DanielFloresElias/MinairoV1.0/DOCs/CatSkills2023/Modul_1/PistaDemo.PNG

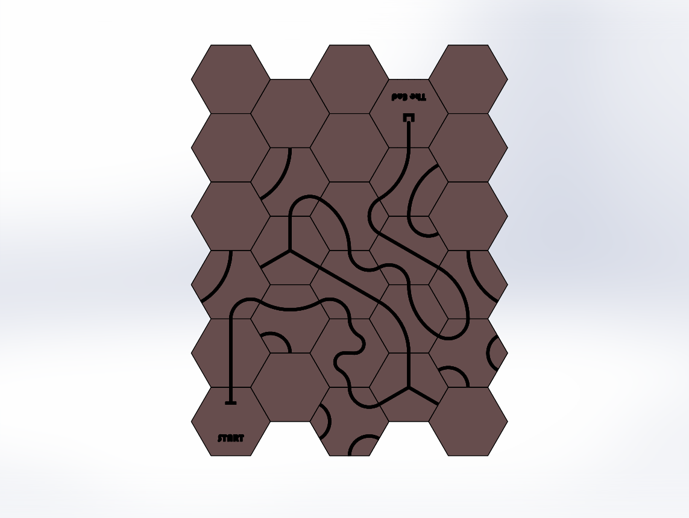
DOCs/CatSkills2023/Modul_1/PistaDemo.PNG
