DanielFloresElias/MinairoV1.0/Hardware/Firmware/Slave0_Sensors/Documents/Pololu Driverjpg.jpg

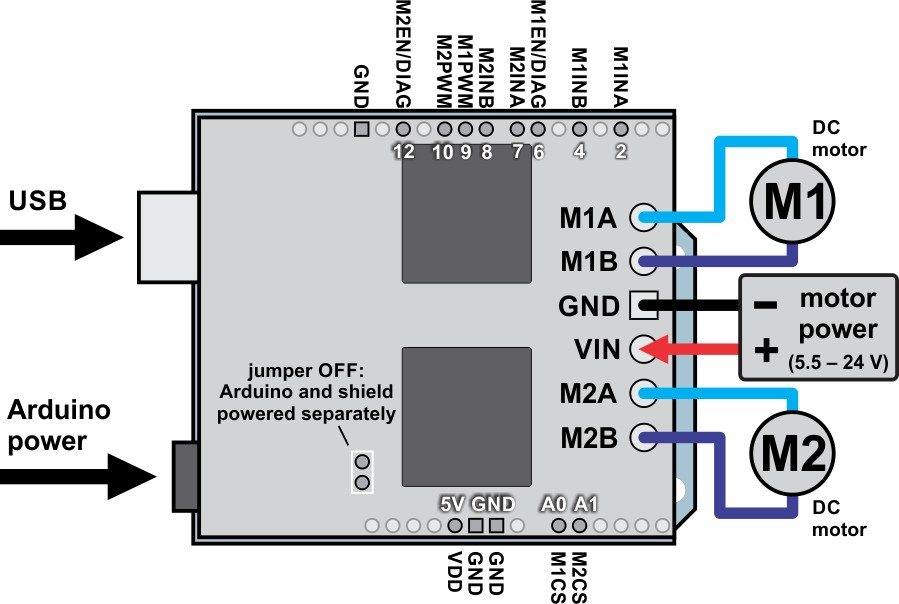
Hardware/Firmware/Slave0_Sensors/Documents/Pololu Driverjpg.jpg
