DanielFloresElias/MinairoV1.0/Hardware/Firmware/Slave0_Sensors/Documents/WhatsApp Image 2022-01-12 at 19.06.40.jpeg

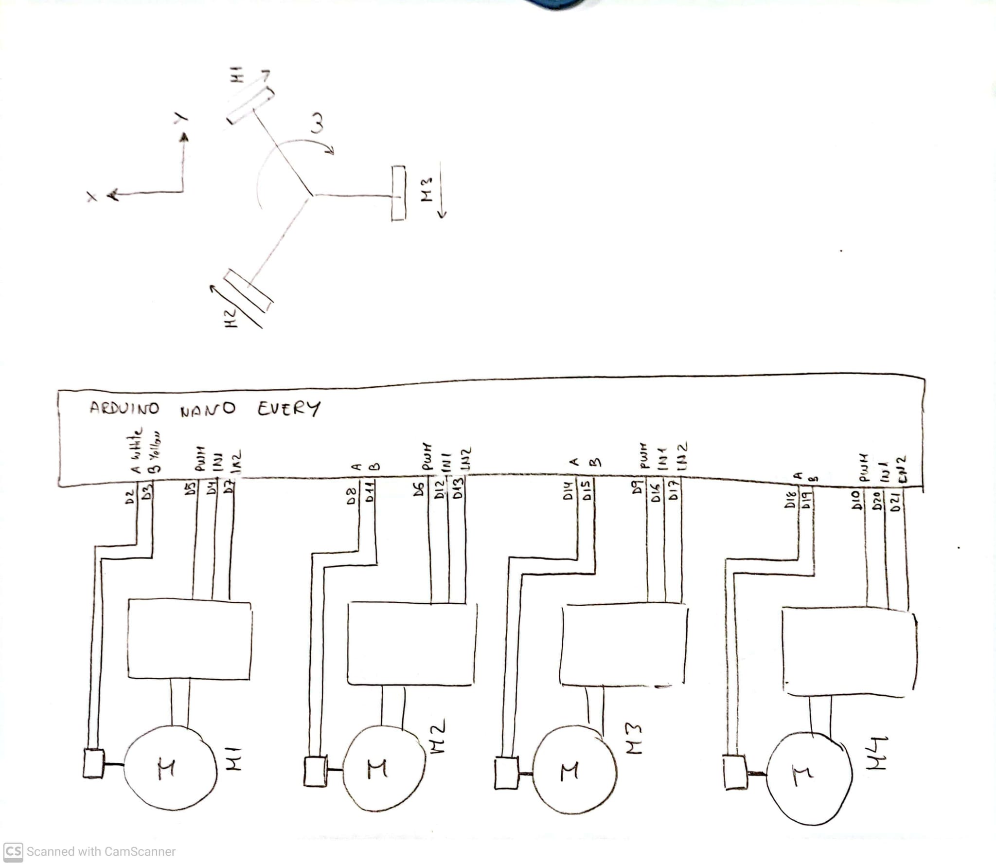
Hardware/Firmware/Slave0_Sensors/Documents/WhatsApp Image 2022-01-12 at 19.06.40.jpeg
