DanielFloresElias/MinairoV1.0/Hardware/STLs/Llapis/IMG/img_pen03.jpeg

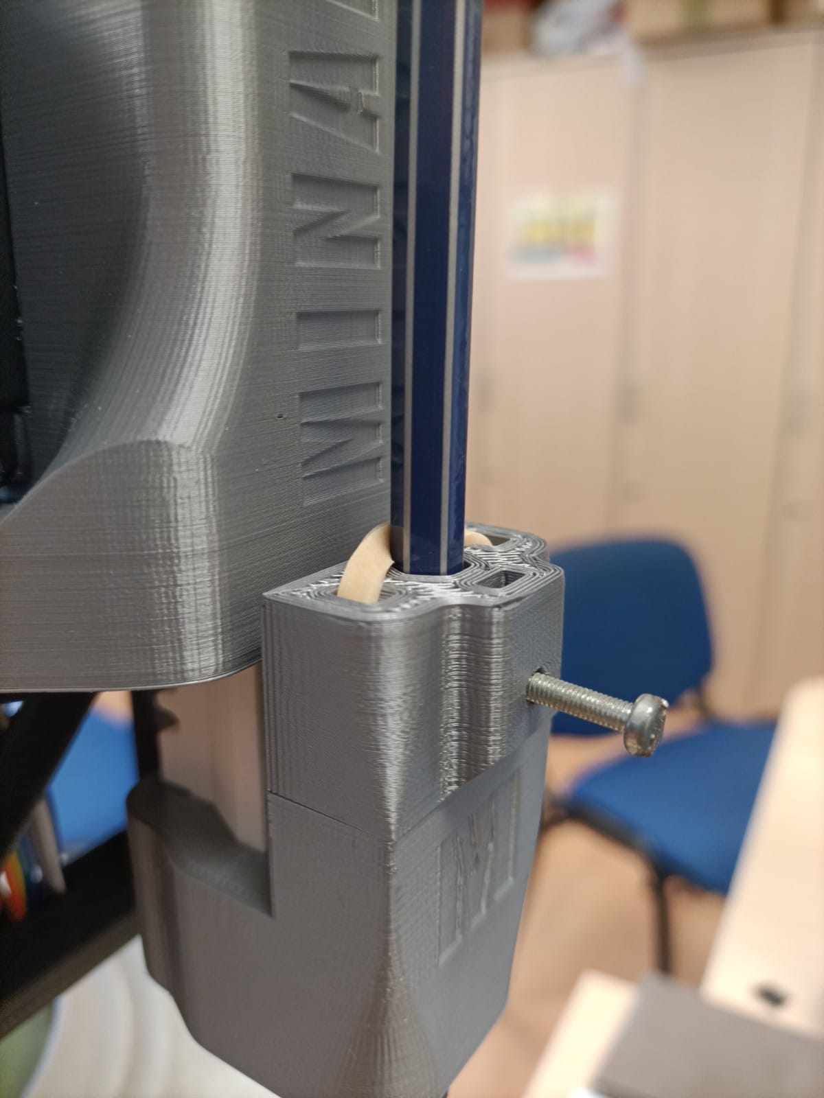
Hardware/STLs/Llapis/IMG/img_pen03.jpeg
