DanielFloresElias/MinairoV1.0/IMG/BackSide.png

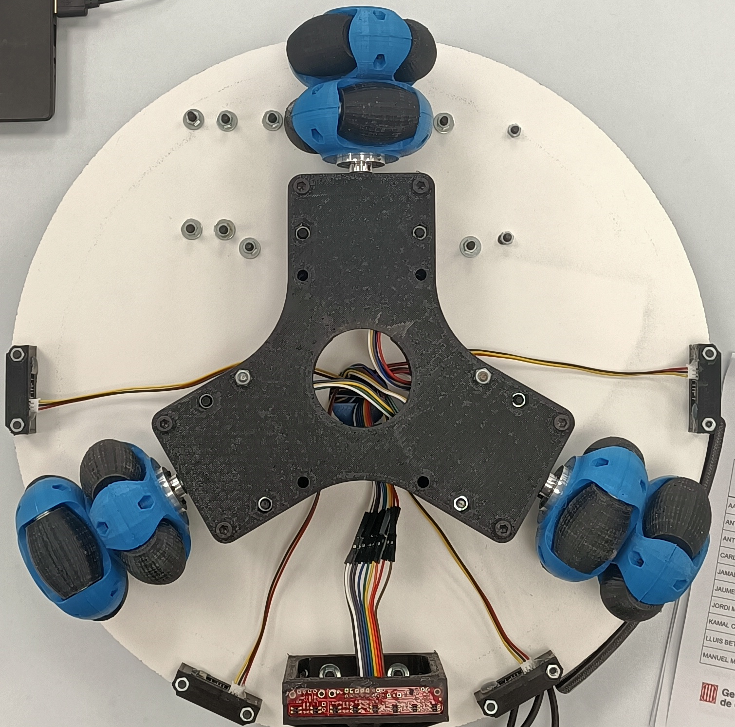
IMG/BackSide.png
