DanielFloresElias/MinairoV1.0/IMG/bateria-cecotec-conga-excellence-990.jpg

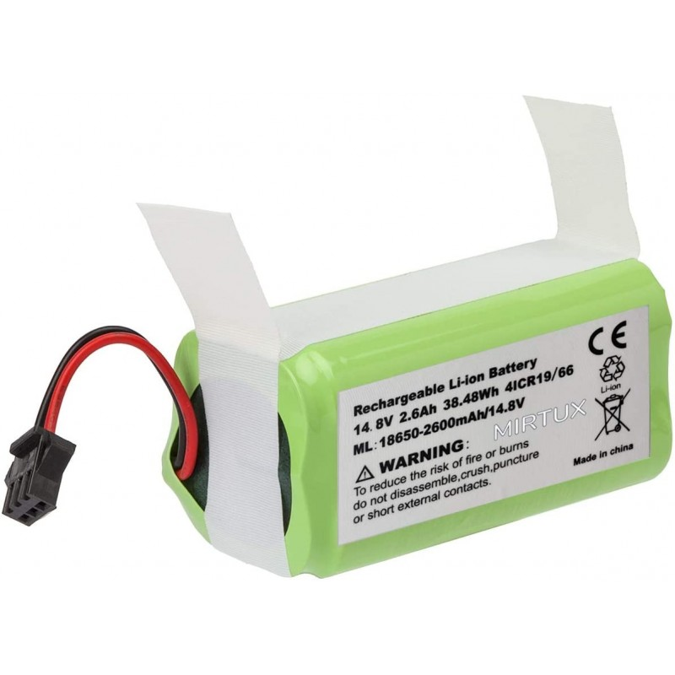
IMG/bateria-cecotec-conga-excellence-990.jpg
