DanielFloresElias/MinairoV1.0/IMG/ESP32-wroom 32.PNG

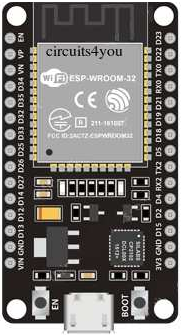
IMG/ESP32-wroom 32.PNG
