DanielFloresElias/MinairoV1.0/IMG/level-shifter-esquema.png

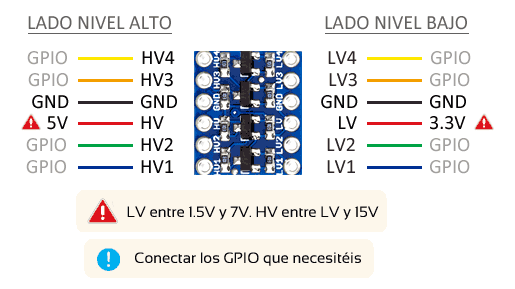
IMG/level-shifter-esquema.png
