DanielFloresElias/MinairoV1.0/IMG/line sensor.jpg

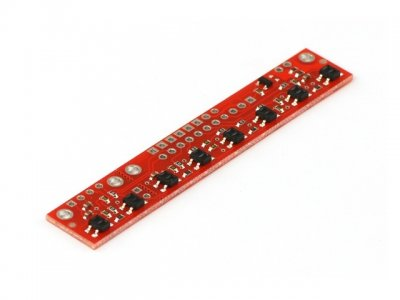
IMG/line sensor.jpg
