DanielFloresElias/MinairoV1.0/IMG/LineSensorArray_Pololu.png

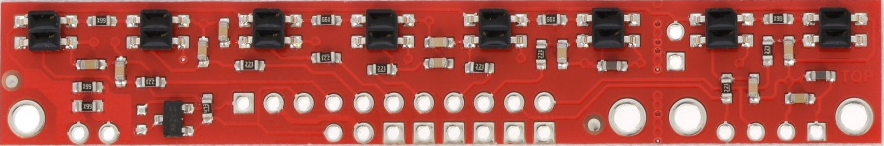
IMG/LineSensorArray_Pololu.png
