DanielFloresElias/MinairoV1.0/IMG/Minairo_1.0.png

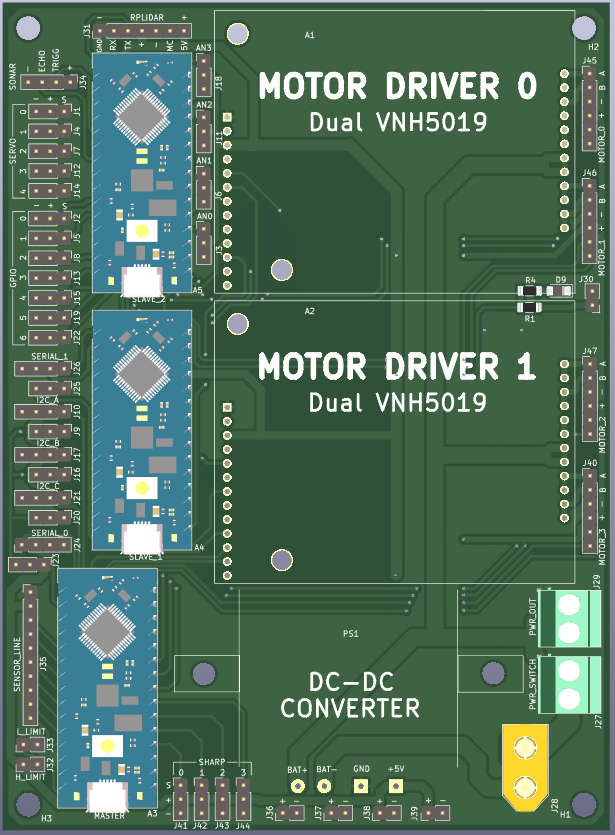
IMG/Minairo_1.0.png
