DanielFloresElias/MinairoV1.0/IMG/Minairo_img01.png

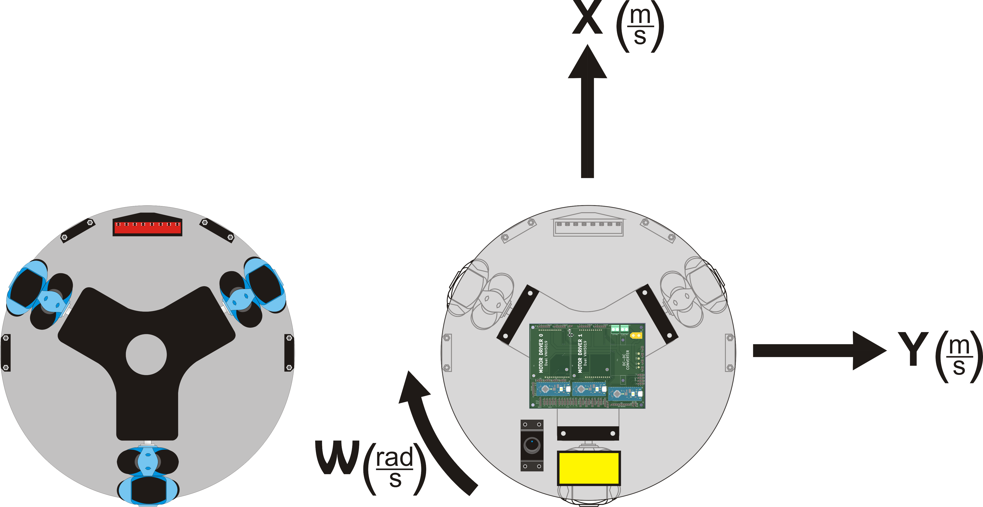
IMG/Minairo_img01.png
