DanielFloresElias/MinairoV1.0/IMG/Minairo_img02.png

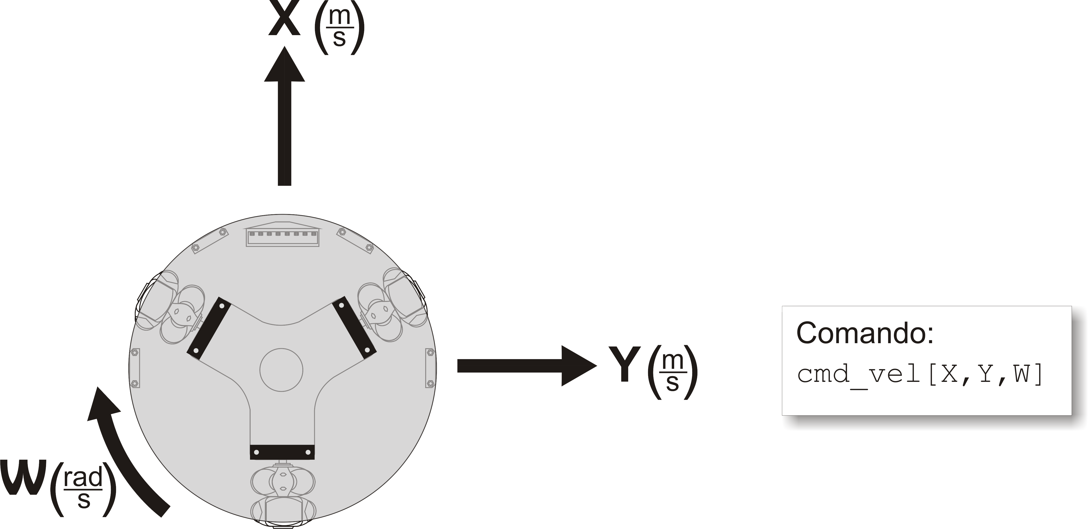
IMG/Minairo_img02.png
