DanielFloresElias/MinairoV1.0/IMG/Minairó_Front.png

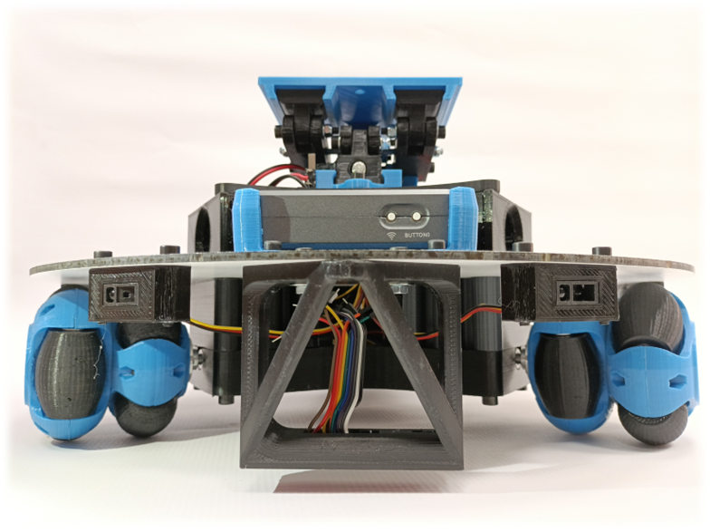
IMG/Minairó_Front.png
