DanielFloresElias/MinairoV1.0/IMG/Minairó_Front_transp.png

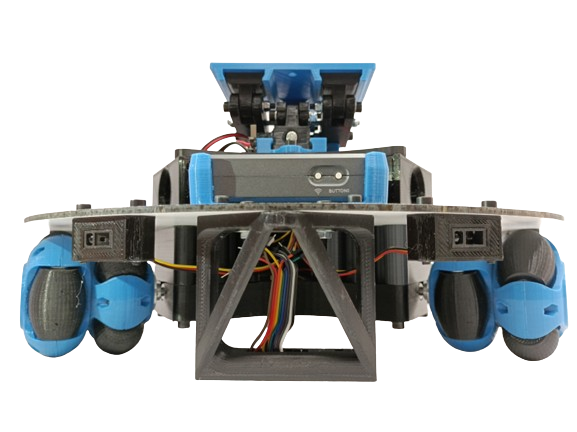
IMG/Minairó_Front_transp.png
