DanielFloresElias/MinairoV1.0/IMG/Minairó_img03.png

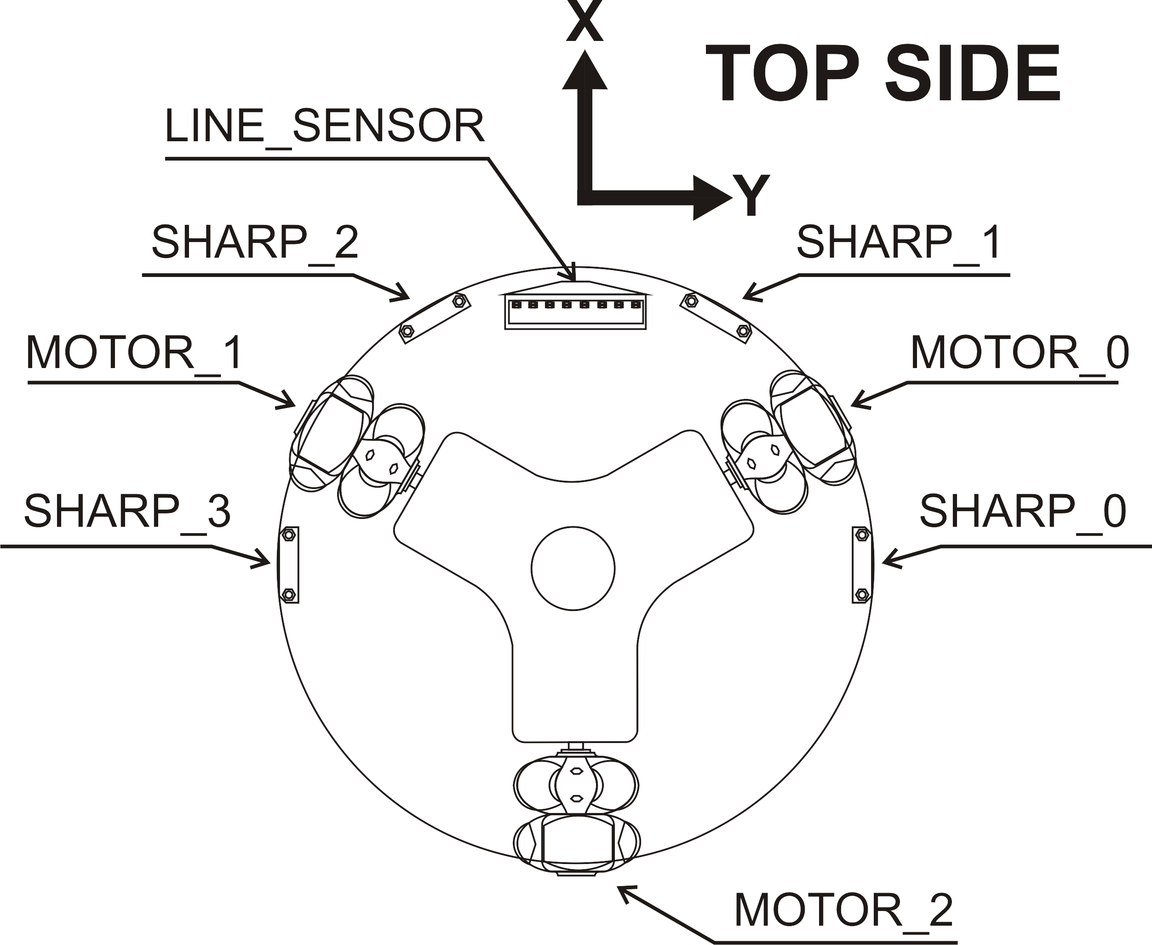
IMG/Minairó_img03.png
