DanielFloresElias/MinairoV1.0/IMG/Minairó_img04.png

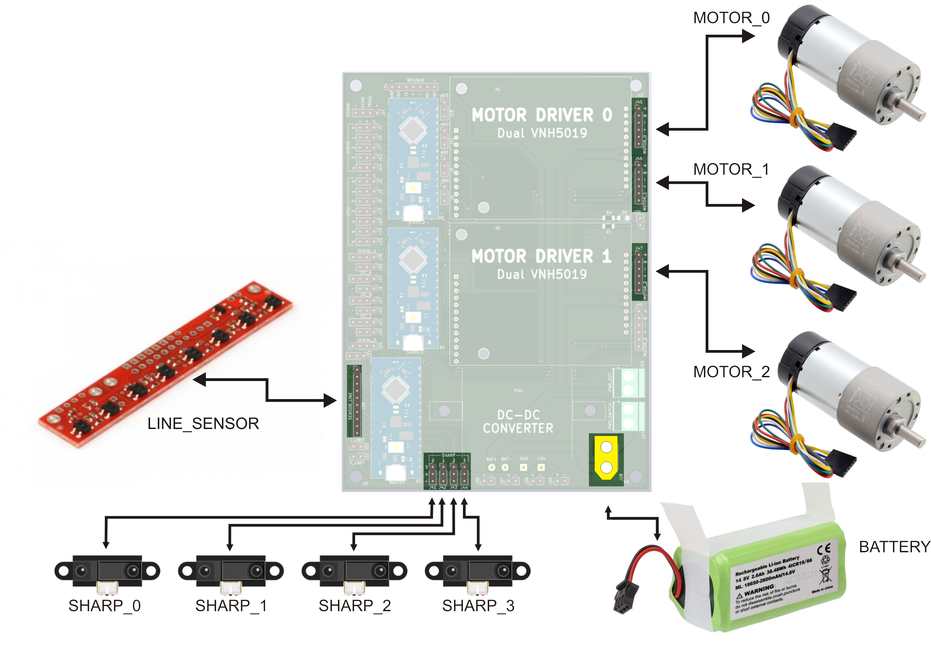
IMG/Minairó_img04.png
