DanielFloresElias/MinairoV1.0/IMG/Minairó_img05.png

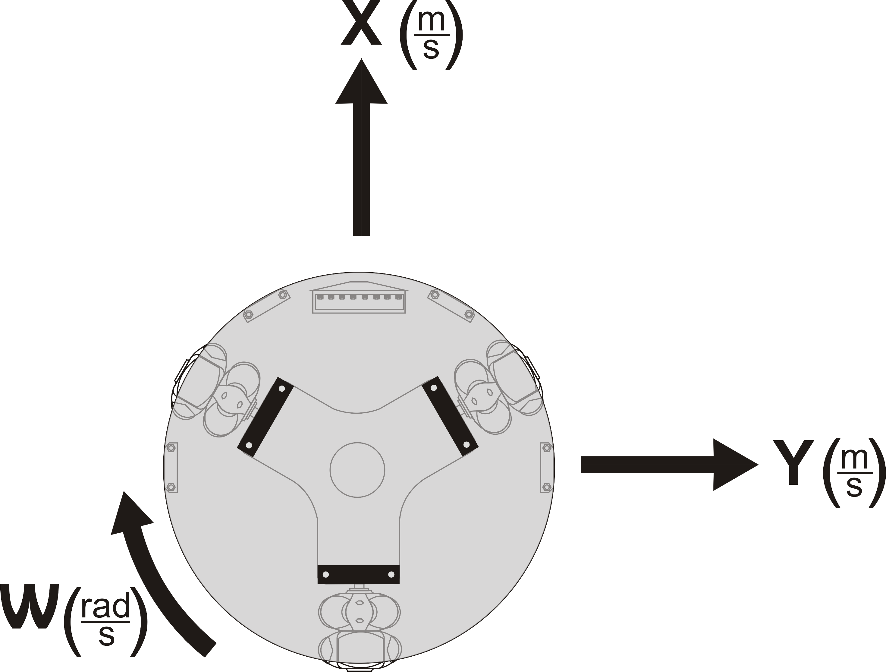
IMG/Minairó_img05.png
