DanielFloresElias/MinairoV1.0/IMG/MotorPololu.jpg

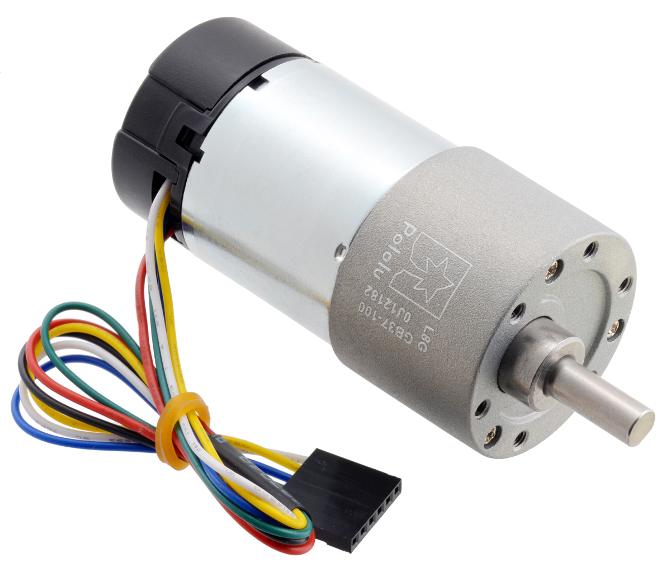
IMG/MotorPololu.jpg
