DanielFloresElias/MinairoV1.0/Hardware/Components/Regulador/regulador-dc-dc-12-24v-a-5v-5a.jpg

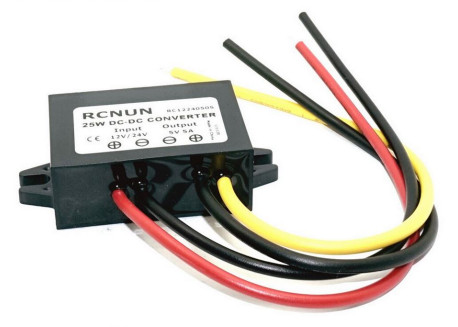
Hardware/Components/Regulador/regulador-dc-dc-12-24v-a-5v-5a.jpg
